Resinchem/Analog-LED-Clock/src/Credentials.h

#define SID "YOUR_WIFI_SSID"           // Enter your WiFI SSID (keep the quotes where shown)    
#define PW "YOUR_WIFI_PASSWORD"        // Enter your WiFi Password 
#define MQTTUSERNAME "MQTT_USER"       // Enter your MQTT User Name for your MQTT Broker
#define MQTTPWD "MQTT_PASSWORD"        // Enter your MQTT User Password 
#define MQTTSERVER "192.168.1.108"     // IP Address (or url) of MQTT Broker. Use '0.0.0.0' if not enabling MQTT
#define MQTTPORT 1883                  // Port of MQTT Broker.  This is usually 1883
#define AP_SSID "analog_clock"         // Local AP to broadcast for WIFIMODE 0 or 2 (see Settings.h) (normally broadcasts on 192.168.4.1)
#define AP_PWD "hot_spot_pw"           // Password for local AP mode - change to whatever you like
